DreaM117er/Explorer-Keyboard-Mountian/pic/RB_B.png

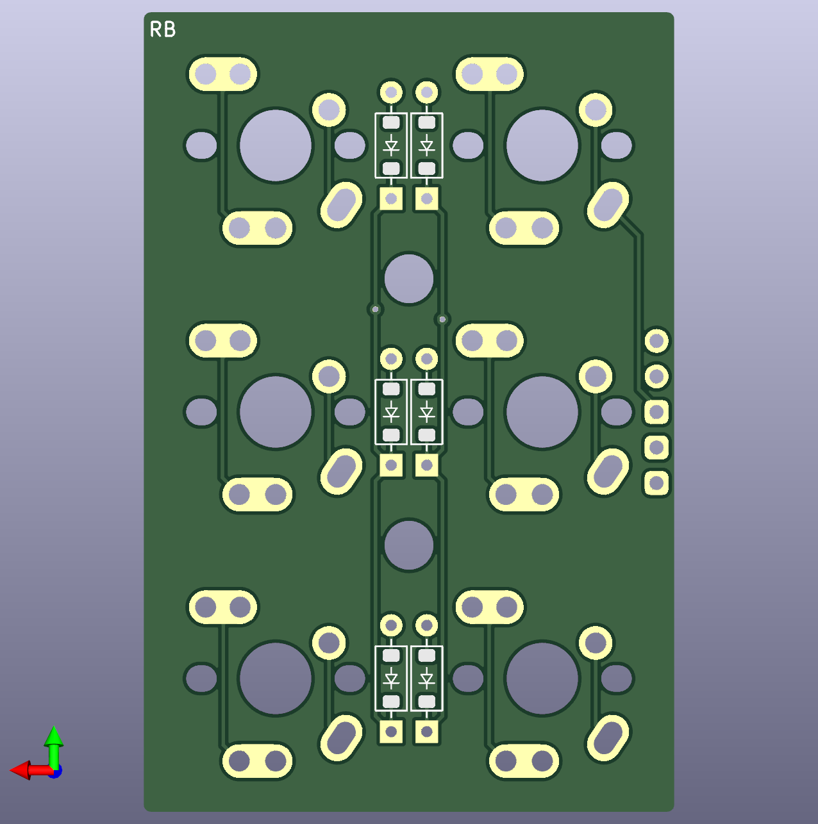
pic/RB_B.png
